JeremyProffitt/10-inch-unibody-rack/assets/waveshare-7inch-lcd-case-portrait_front.png

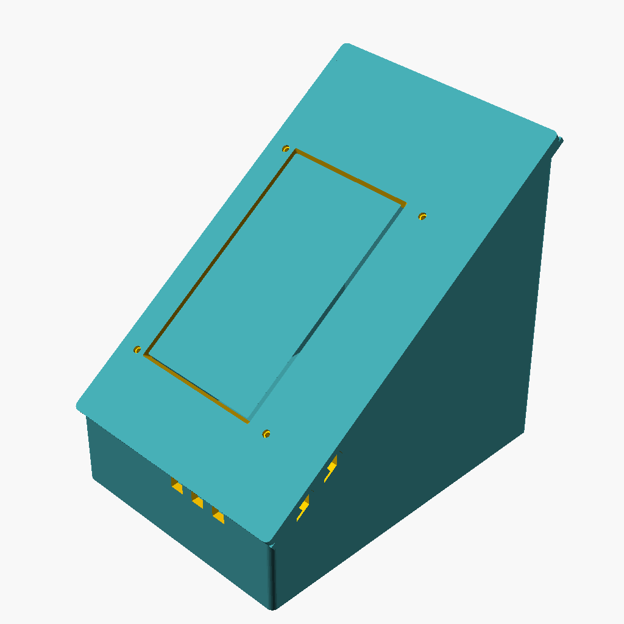
assets/waveshare-7inch-lcd-case-portrait_front.png
